rmingon/hexapod/stl/Tibia_Bracket_End_Cap.stl

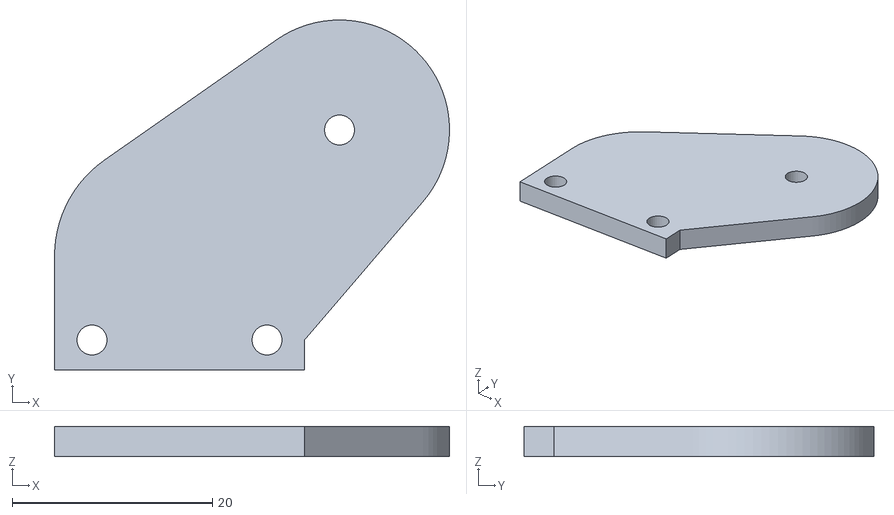
[picture p19: CAD file, 2023-01-02]
stl/Tibia_Bracket_End_Cap.stl
39.5 x 35.0 x 3.00
