rmingon/hexapod/stl/Wire_Guide.stl

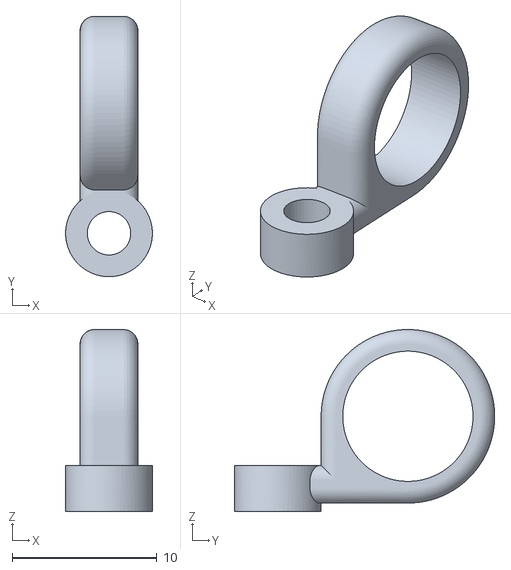
[picture p20: CAD file, 2023-01-02]
stl/Wire_Guide.stl
6.00 x 18.0 x 12.6
