rmingon/hexapod/stl/SBEC_Holder.stl

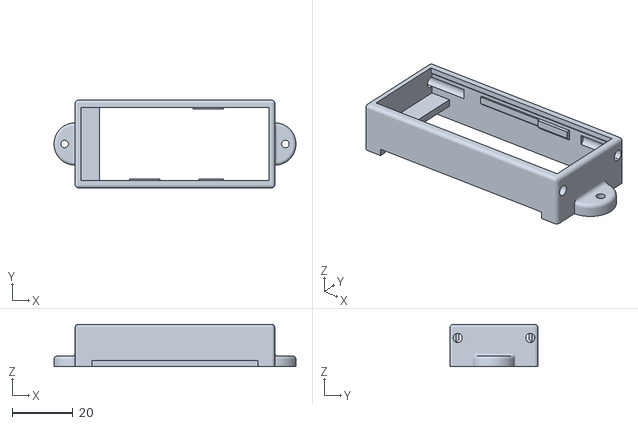
[picture p21: CAD file, 2023-01-02]
stl/SBEC_Holder.stl
80.0 x 29.0 x 14.0
