rmingon/hexapod/stl/Femur_Bracket_End_Cap.stl

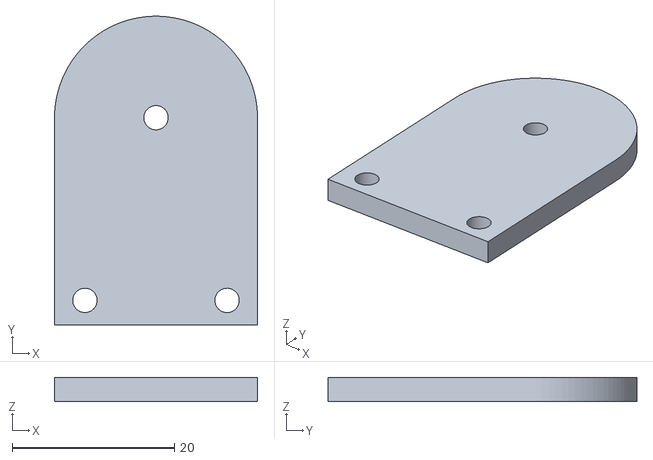
[picture p22: CAD file, 2023-01-02]
stl/Femur_Bracket_End_Cap.stl
25.0 x 38.0 x 3.00
